SergioRibera/crkbd/pcbs/cherry-wireless/common/left.kicad_sch

## KiCad design pcbs/cherry-wireless/common/left.kicad_sch (2024-08-09)

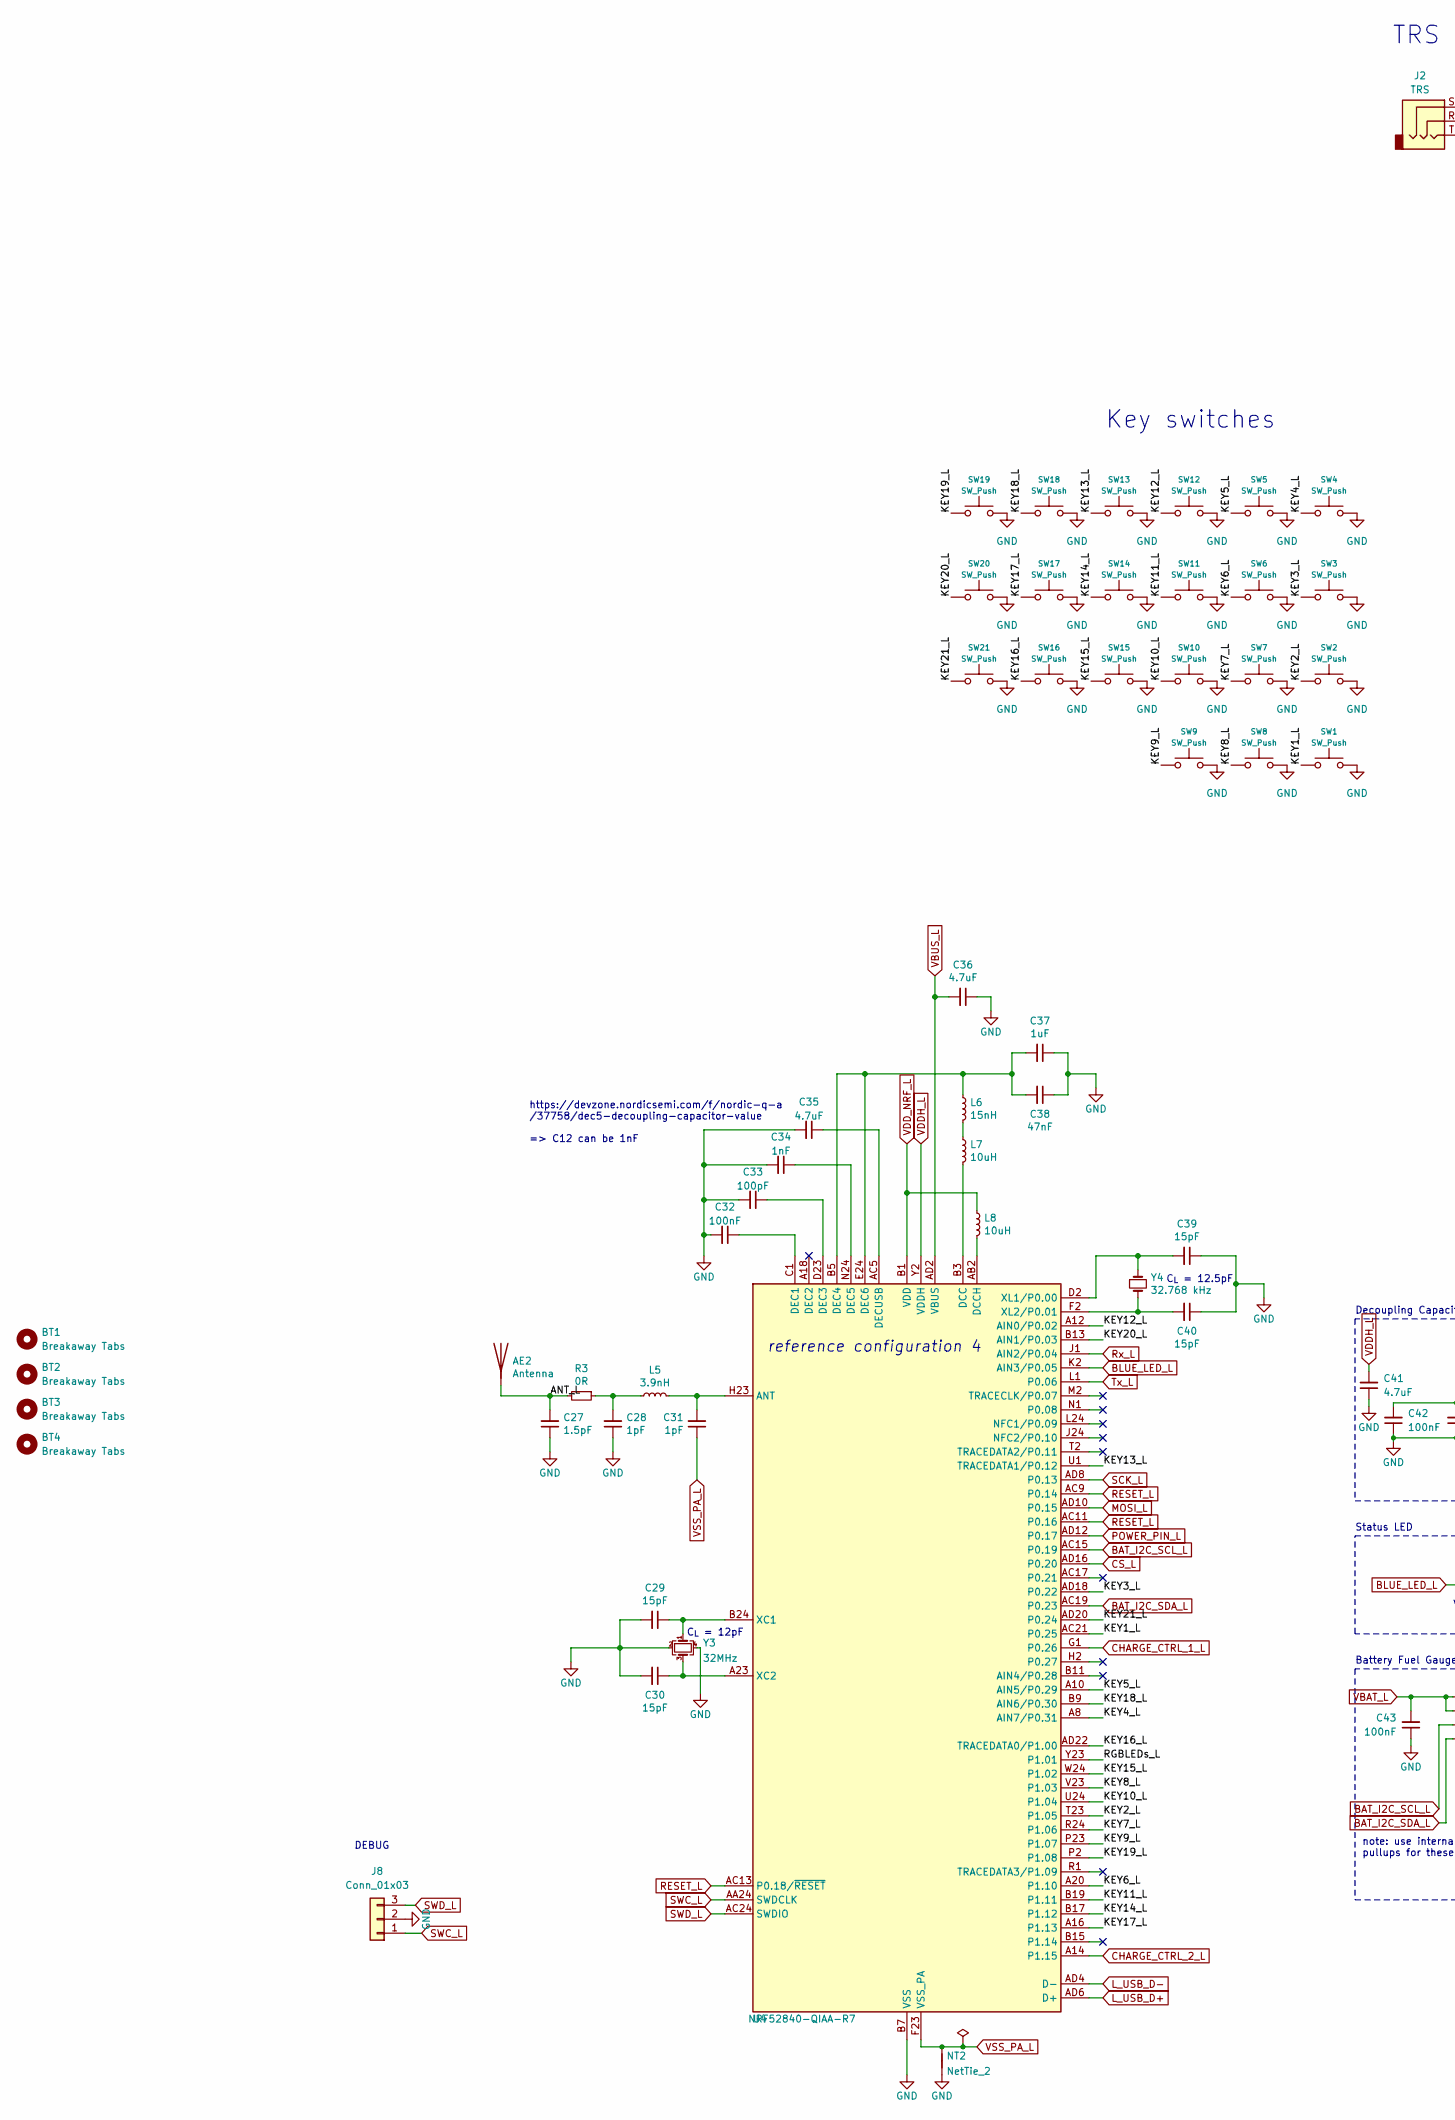
[picture p6: schematic left.kicad_sch, part in row 1, column 1]

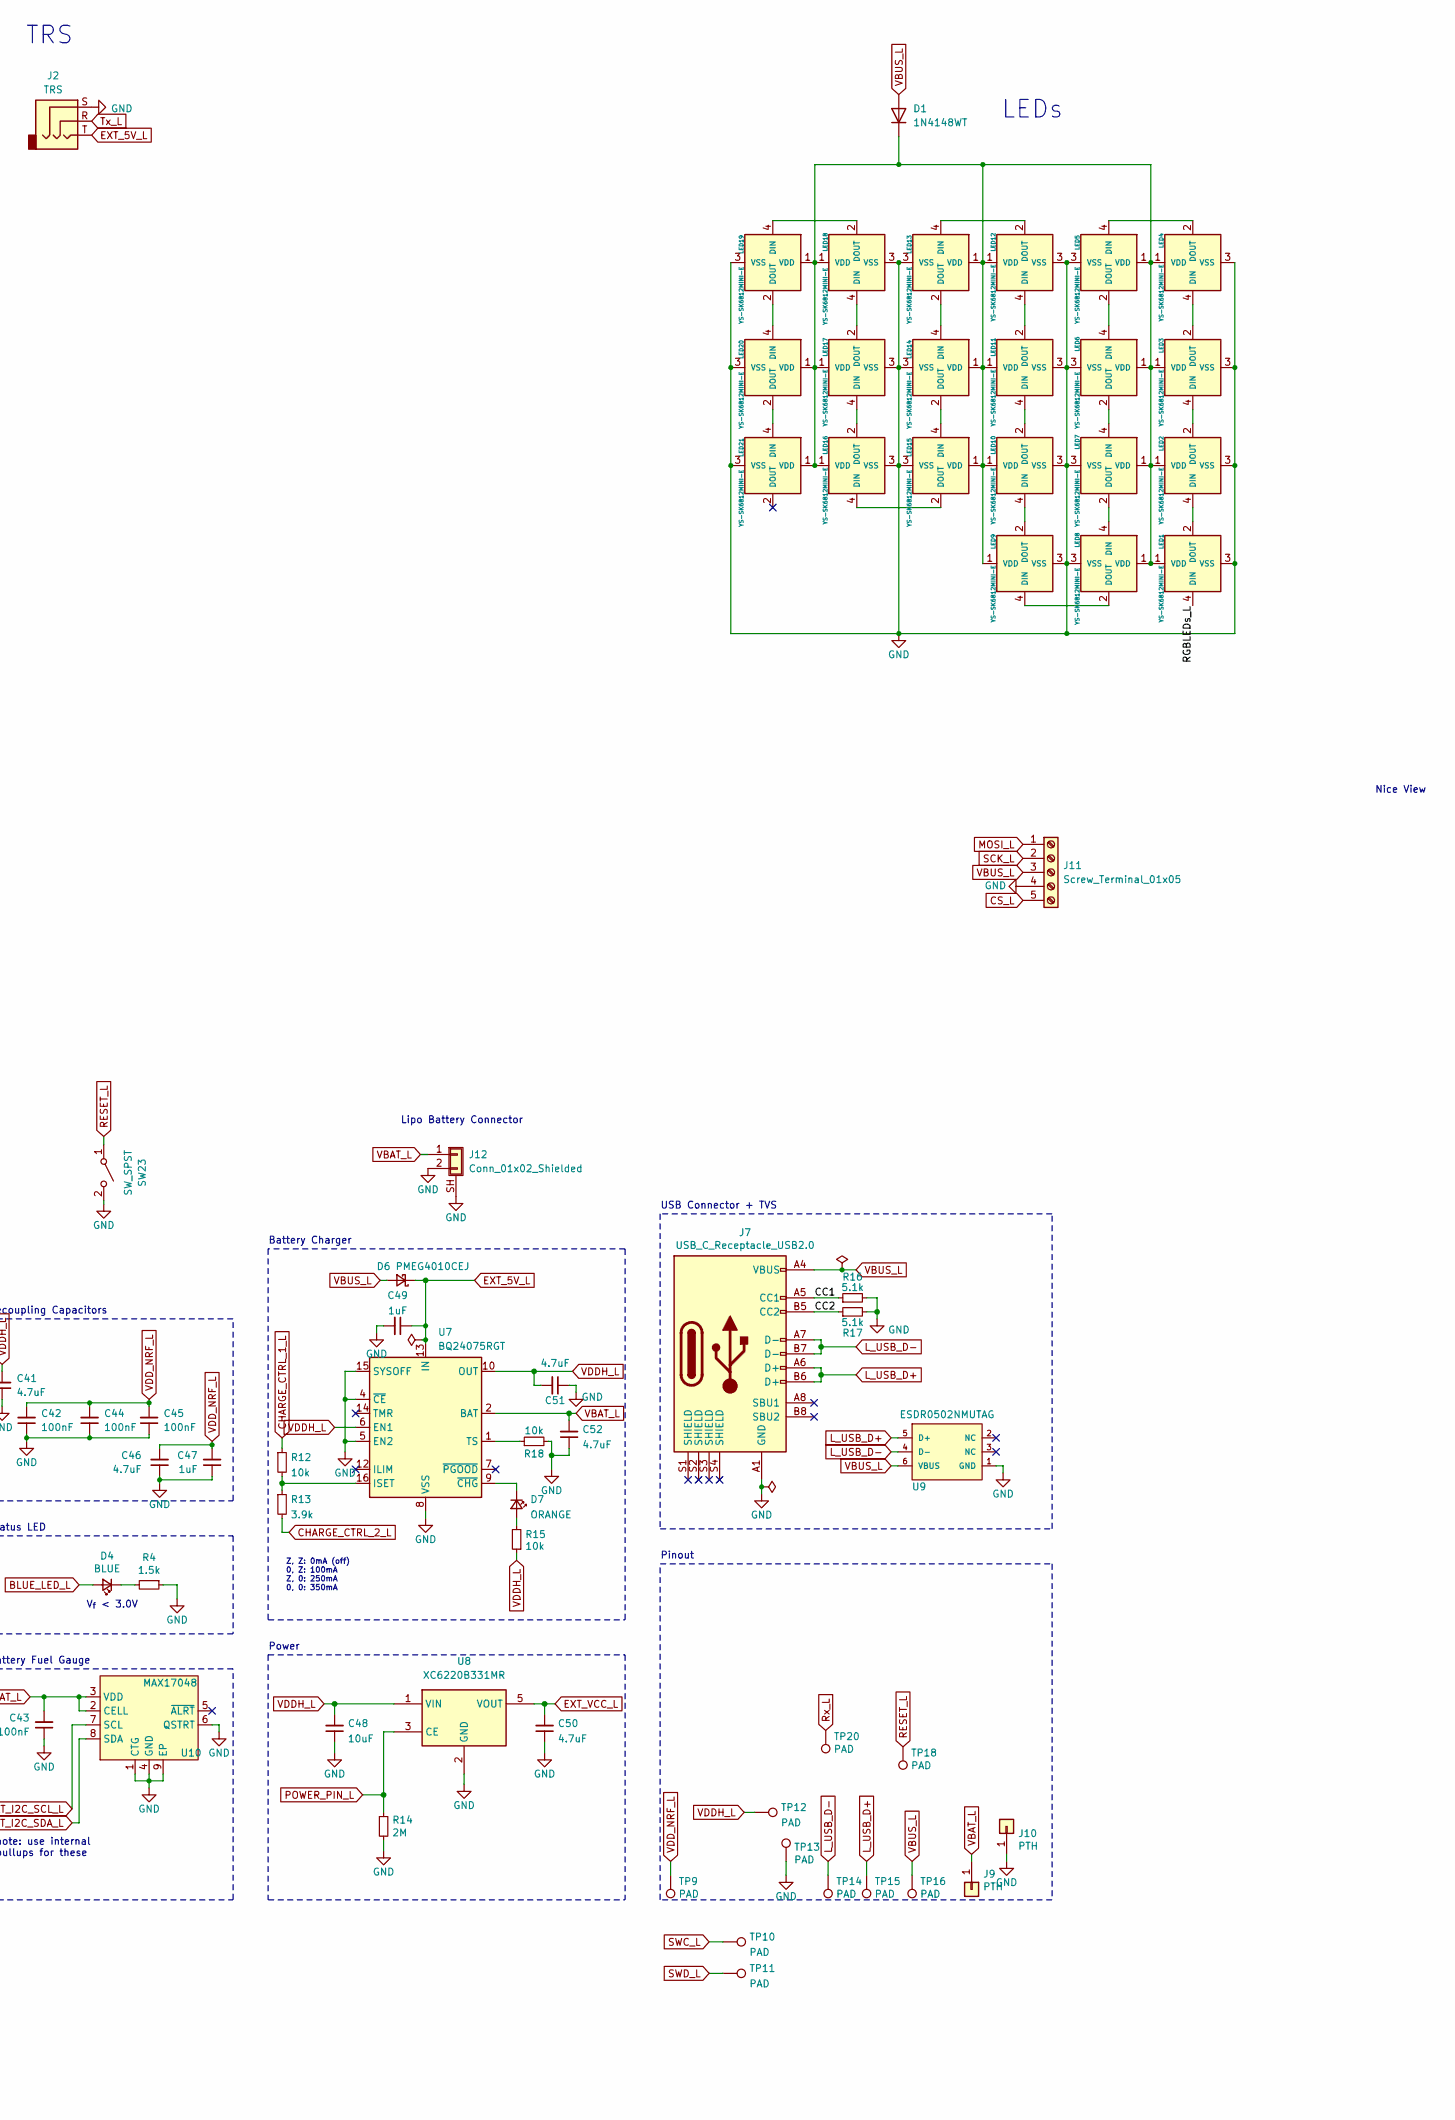
[picture p7: schematic left.kicad_sch, part in row 1, column 2]

Parts:
AE2: Antenna; 2.4GHz-meander-antenna-v2
BT1, BT2, BT3, BT4: Breakaway Tabs; Breakaway_Tabs
C27: 1.5pF; C_0402_1005Metric; JLC Part C1552
C28, C31: 1pF; C_0402_1005Metric; JLC Part C1550
C29, C30, C39, C40: 15pF; C_0402_1005Metric; JLC Part C1548
C32, C42, C43, C44, C45: 100nF; C_0402_1005Metric; JLC Part C1525
C33: 100pF; C_0402_1005Metric; JLC Part C1546
C34: 1nF; C_0402_1005Metric; JLC Part C1523
C35, C36, C41, C46, C50, C51, C52: 4.7uF; C_0402_1005Metric; JLC Part C23733
C37, C47, C49: 1uF; C_0402_1005Metric; JLC Part C52923
C38: 47nF; C_0402_1005Metric; JLC Part C312032
C48: 10uF; C_0603_1608Metric; JLC Part C19702
D1: 1N4148WT; D_SOD-523; JLC Part C232841
D4: BLUE; LED_0402_1005Metric; JLC Part C364550
D6: PMEG4010CEJ; D_SOD-323F; JLC Part C50704
D7: ORANGE; LED_0402_1005Metric; JLC Part C364554
J2: TRS; PJ-398A-5A_PJ-399B-6A; JLC Part C128994
J7: USB_C_Receptacle_USB2.0; USB-C_C168688; JLC Part C168688
J8: Conn_01x03; PinHeader_1x03_P2.54mm_Vertical
J9, J10: PTH; PTH-0.8_0.45mm
J11: Screw_Terminal_01x05; PinHeader_1x05_P2.54mm_Vertical
J12: Conn_01x02_Shielded; CONN-SMD_SM02B-PASS-TLFSN; JLC Part C495198
L5: 3.9nH; L_0402_1005Metric; JLC Part C14033
L6: 15nH; L_0402_1005Metric; JLC Part C27143
L7, L8: 10uH; L_0603_1608Metric; JLC Part C1035
LED1, LED2, LED3, LED4, LED5, LED6, LED7, LED8, LED9, LED10, LED11, LED12, LED13, LED14, LED15, LED16, LED17, LED18, LED19, LED20, LED21: YS-SK6812MINI-E; YS-SK6812MINI-E_crone; JLC Part C5149201
NT2: NetTie_2; net-tie-2-tiny
R3: 0R; R_0402_1005Metric; JLC Part C17168
R4: 1.5k; R_0402_1005Metric; JLC Part C25867
R12, R15, R18: 10k; R_0402_1005Metric; JLC Part C25744
R13: 3.9k; R_0402_1005Metric; JLC Part C51721
R14: 2M; R_0402_1005Metric; JLC Part C138014
R16, R17: 5.1k; R_0402_1005Metric; JLC Part C25905
SW1: SW_Push; keyswitch_cherrymx_hotswap_1.5u; JLC Part C2803348
SW2, SW3, SW4, SW5, SW6, SW7, SW8, SW9, SW10, SW11, SW12, SW13, SW14, SW15, SW16, SW17, SW18, SW19, SW20, SW21: SW_Push; keyswitch_cherrymx_hotswap_1u; JLC Part C2803348
SW23: SW_SPST; SW-SMD-TS-1088-AR02016
TP9, TP10, TP11, TP12, TP13, TP14, TP15, TP16, TP18, TP20: PAD; TestPoint_Pad_1.0x1.0mm-nosilk
U4: NRF52840-QIAA-R7; AQFN-73-1EP_7x7mm_P0.5mm_NRF52840-custom; JLC Part C1851953
U7: BQ24075RGT; VQFN-16-1EP_3x3mm_P0.5mm_EP1.6x1.6mm; JLC Part C2865459
U8: XC6220B331MR; TSOT-23-5; JLC Part C86534
U9: ESDR0502NMUTAG; UDFN-6_1.2x1.0mm_P0.4mm; JLC Part C327480
U10: MAX17048; TDFN-8-1EP_2x2mm_P0.5mm_EP0.8x1.2mm; JLC Part C2682616
Y3: 32MHz; Crystal_SMD_2016-4Pin_2.0x1.6mm; JLC Part C255896
Y4: 32.768 kHz; Crystal_SMD_2012-2Pin_2.0x1.2mm; JLC Part C93231

Connections:
ANT_L: AE2.1, C27.2, R3.2
BAT_I2C_SCL_L: U4.AC15 (P0.19), U10.7 (SCL)
BAT_I2C_SDA_L: U4.AC19 (P0.23), U10.8 (SDA)
BLUE_LED_L: D4.2 (A), U4.K2 (AIN3/P0.05)
CC1: J7.A5 (CC1), R16.1
CC2: J7.B5 (CC2), R17.1
CHARGE_CTRL_1_L: R12.1, U4.G1 (P0.26)
CHARGE_CTRL_2_L: R13.2, U4.A14 (P1.15)
CS_L: J11.5, U4.AD16 (P0.20)
EXT_5V_L: C49.1, D6.1 (K), J2.T, U7.13 (IN)
EXT_VCC_L: C50.2, U8.5 (VOUT)
GND: C27.1, C28.1, C29.2, C30.2, C32.2, C33.2, C34.2, C35.2, C36.1, C37.1, C38.1, C39.1, C40.1, C41.1, C42.1, C43.1, C44.1, C45.1, C46.1, C47.1, C48.1, C49.2, C50.1, C51.1, C52.1, J2.S, J7.A1 (GND), J8.2, J10.1, J11.4, J12.2, J12.SH (Shield), LED1.3 (VSS), LED2.3 (VSS), LED3.3 (VSS), LED4.3 (VSS), LED5.3 (VSS), LED6.3 (VSS), LED7.3 (VSS), LED8.3 (VSS), LED9.3 (VSS), LED10.3 (VSS), LED11.3 (VSS), LED12.3 (VSS), LED13.3 (VSS), LED14.3 (VSS), LED15.3 (VSS), LED16.3 (VSS), LED17.3 (VSS), LED18.3 (VSS), LED19.3 (VSS), LED20.3 (VSS), LED21.3 (VSS), NT2.2, R4.1, R14.2, R16.2, R17.2, R18.2, SW1.2, SW2.2, SW3.2, SW4.2, SW5.2, SW6.2, SW7.2, SW8.2, SW9.2, SW10.2, SW11.2, SW12.2, SW13.2, SW14.2, SW15.2, SW16.2, SW17.2, SW18.2, SW19.2, SW20.2, SW21.2, SW23.2 (B), TP13.1, U4.B7 (VSS), U4.EP (VSS), U7.4 (~CE), U7.5 (EN2), U7.8 (VSS), U7.15 (SYSOFF), U7.17 (VSS), U8.2 (GND), U9.1 (GND), U10.1 (CTG), U10.4 (GND), U10.6 (QSTRT), U10.9 (EP), Y3.2, Y3.4
KEY1_L: SW1.1, U4.AC21 (P0.25)
KEY2_L: SW2.1, U4.T23 (P1.05)
KEY3_L: SW3.1, U4.AD18 (P0.22)
KEY4_L: SW4.1, U4.A8 (AIN7/P0.31)
KEY5_L: SW5.1, U4.A10 (AIN5/P0.29)
KEY6_L: SW6.1, U4.A20 (P1.10)
KEY7_L: SW7.1, U4.R24 (P1.06)
KEY8_L: SW8.1, U4.V23 (P1.03)
KEY9_L: SW9.1, U4.P23 (P1.07)
KEY10_L: SW10.1, U4.U24 (P1.04)
KEY11_L: SW11.1, U4.B19 (P1.11)
KEY12_L: SW12.1, U4.A12 (AIN0/P0.02)
KEY13_L: SW13.1, U4.U1 (TRACEDATA1/P0.12)
KEY14_L: SW14.1, U4.B17 (P1.12)
KEY15_L: SW15.1, U4.W24 (P1.02)
KEY16_L: SW16.1, U4.AD22 (TRACEDATA0/P1.00)
KEY17_L: SW17.1, U4.A16 (P1.13)
KEY18_L: SW18.1, U4.B9 (AIN6/P0.30)
KEY19_L: SW19.1, U4.P2 (P1.08)
KEY20_L: SW20.1, U4.B13 (AIN1/P0.03)
KEY21_L: SW21.1, U4.AD20 (P0.24)
L_USB_D+: J7.A6 (D+), J7.B6 (D+), TP15.1, U4.AD6 (D+), U9.5 (D+)
L_USB_D-: J7.A7 (D-), J7.B7 (D-), TP14.1, U4.AD4 (D-), U9.4 (D-)
MOSI_L: J11.1, U4.AD10 (P0.15)
unnamed: C28.2, L5.1, R3.1
unnamed: C29.1, U4.B24 (XC1), Y3.1
unnamed: C30.1, U4.A23 (XC2), Y3.3
unnamed: C31.2, L5.2, U4.H23 (ANT)
unnamed: C32.1, U4.C1 (DEC1)
unnamed: C33.1, U4.D23 (DEC3)
unnamed: C34.1, U4.N24 (DEC5)
unnamed: C35.1, U4.AC5 (DECUSB)
unnamed: C37.2, C38.2, L6.1, U4.B5 (DEC4), U4.E24 (DEC6)
unnamed: C39.2, U4.D2 (XL1/P0.00), Y4.1
unnamed: C40.2, U4.F2 (XL2/P0.01), Y4.2
unnamed: D1.1 (K), LED1.1 (VDD), LED2.1 (VDD), LED3.1 (VDD), LED4.1 (VDD), LED5.1 (VDD), LED6.1 (VDD), LED7.1 (VDD), LED8.1 (VDD), LED9.1 (VDD), LED10.1 (VDD), LED11.1 (VDD), LED12.1 (VDD), LED13.1 (VDD), LED14.1 (VDD), LED15.1 (VDD), LED16.1 (VDD), LED17.1 (VDD), LED18.1 (VDD), LED19.1 (VDD), LED20.1 (VDD), LED21.1 (VDD)
unnamed: D4.1 (K), R4.2
unnamed: D7.1 (K), U7.9 (~CHG)
unnamed: D7.2 (A), R15.2
unnamed: L6.2, L7.1
unnamed: L7.2, U4.B3 (DCC)
unnamed: L8.2, U4.AB2 (DCCH)
unnamed: LED1.2 (DOUT), LED2.4 (DIN)
unnamed: LED2.2 (DOUT), LED3.4 (DIN)
unnamed: LED3.2 (DOUT), LED4.4 (DIN)
unnamed: LED4.2 (DOUT), LED5.4 (DIN)
unnamed: LED5.2 (DOUT), LED6.4 (DIN)
unnamed: LED6.2 (DOUT), LED7.4 (DIN)
unnamed: LED7.2 (DOUT), LED8.4 (DIN)
unnamed: LED8.2 (DOUT), LED9.4 (DIN)
unnamed: LED10.2 (DOUT), LED11.4 (DIN)
unnamed: LED9.2 (DOUT), LED10.4 (DIN)
unnamed: LED11.2 (DOUT), LED12.4 (DIN)
unnamed: LED12.2 (DOUT), LED13.4 (DIN)
unnamed: LED13.2 (DOUT), LED14.4 (DIN)
unnamed: LED14.2 (DOUT), LED15.4 (DIN)
unnamed: LED15.2 (DOUT), LED16.4 (DIN)
unnamed: LED16.2 (DOUT), LED17.4 (DIN)
unnamed: LED17.2 (DOUT), LED18.4 (DIN)
unnamed: LED18.2 (DOUT), LED19.4 (DIN)
unnamed: LED19.2 (DOUT), LED20.4 (DIN)
unnamed: LED20.2 (DOUT), LED21.4 (DIN)
unnamed: R12.2, R13.1, U7.16 (ISET)
unnamed: R18.1, U7.1 (TS)
POWER_PIN_L: R14.1, U4.AD12 (P0.17), U8.3 (CE)
RESET_L: SW23.1 (A), TP18.1, U4.AC9 (P0.14), U4.AC11 (P0.16), U4.AC13 (P0.18/~RESET)
RGBLEDs_L: LED1.4 (DIN), U4.Y23 (P1.01)
Rx_L: TP20.1, U4.J1 (AIN2/P0.04)
SCK_L: J11.2, U4.AD8 (P0.13)
SWC_L: J8.1, TP10.1, U4.AA24 (SWDCLK)
SWD_L: J8.3, TP11.1, U4.AC24 (SWDIO)
Tx_L: J2.R, U4.L1 (P0.06)
VBAT_L: C43.2, C52.2, J9.1, J12.1, U7.2 (BAT), U7.3 (BAT), U10.2 (CELL), U10.3 (VDD)
VBUS_L: C36.2, D1.2 (A), D6.2 (A), J7.A4 (VBUS), J11.3, TP16.1, U4.AD2 (VBUS), U9.6 (VBUS)
VDDH_L: C41.2, C48.2, C51.2, R15.1, TP12.1, U4.Y2 (VDDH), U7.6 (EN1), U7.10 (OUT), U7.11 (OUT), U8.1 (VIN)
VDD_NRF_L: C42.2, C44.2, C45.2, C46.2, C47.2, L8.1, TP9.1, U4.A22 (VDD), U4.AD14 (VDD), U4.AD23 (VDD), U4.B1 (VDD), U4.W1 (VDD)
VSS_PA_L: C31.1, NT2.1, U4.F23 (VSS_PA)

Notes on the sheet:
Key switches
Battery Fuel Gauge
C_{L} = 12pF
Status LED
Z, Z: 0mA (off) 0, Z: 100mA Z, 0: 250mA 0, 0: 350mA
Lipo Battery Connector
DEBUG
LEDs
note: use internal pullups for these
V_{f} < 3.0V
https://devzone.nordicsemi.com/f/nordic-q-a /37758/dec5-decoupling-capacitor-value => C12 can be 1nF
Decoupling Capacitors
Pinout
TRS
C_{L} = 12.5pF
Power
Battery Charger
Nice View
USB Connector + TVS
reference configuration 4
