SergioRibera/crkbd/pcbs/cherry-wireless/common/right.kicad_sch

## KiCad design pcbs/cherry-wireless/common/right.kicad_sch (2024-08-09)

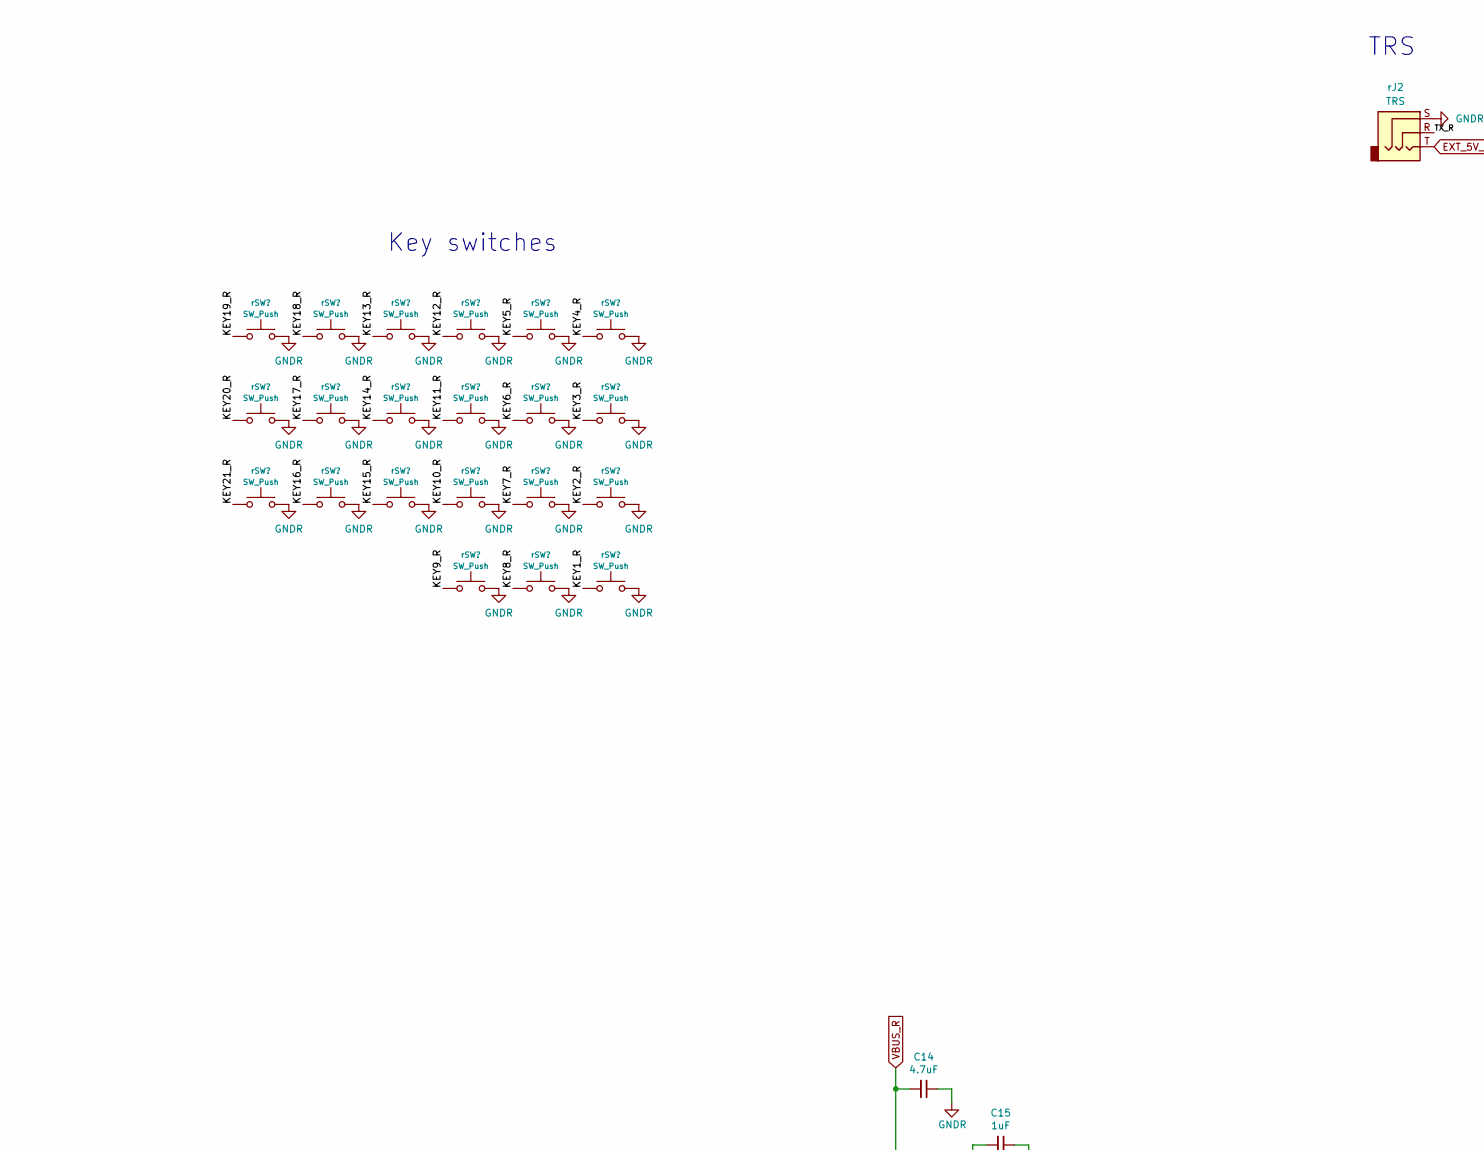
[picture p8: schematic right.kicad_sch, part in row 1, column 1]

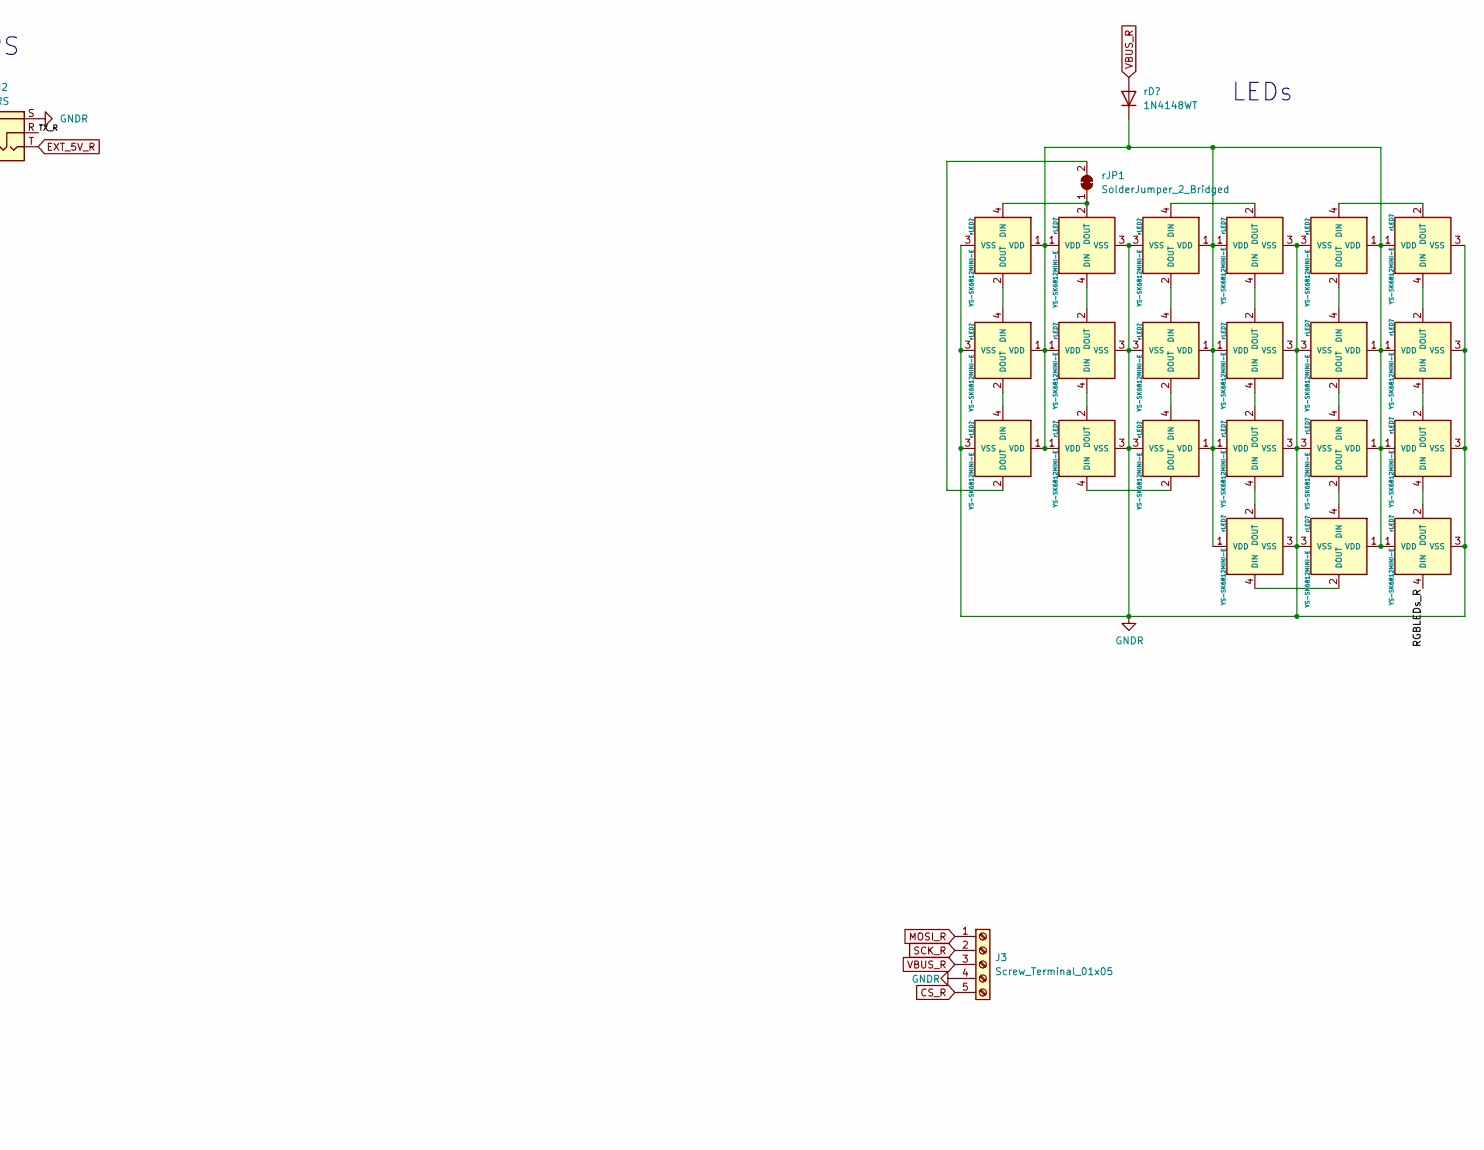
[picture p9: schematic right.kicad_sch, part in row 1, column 2]

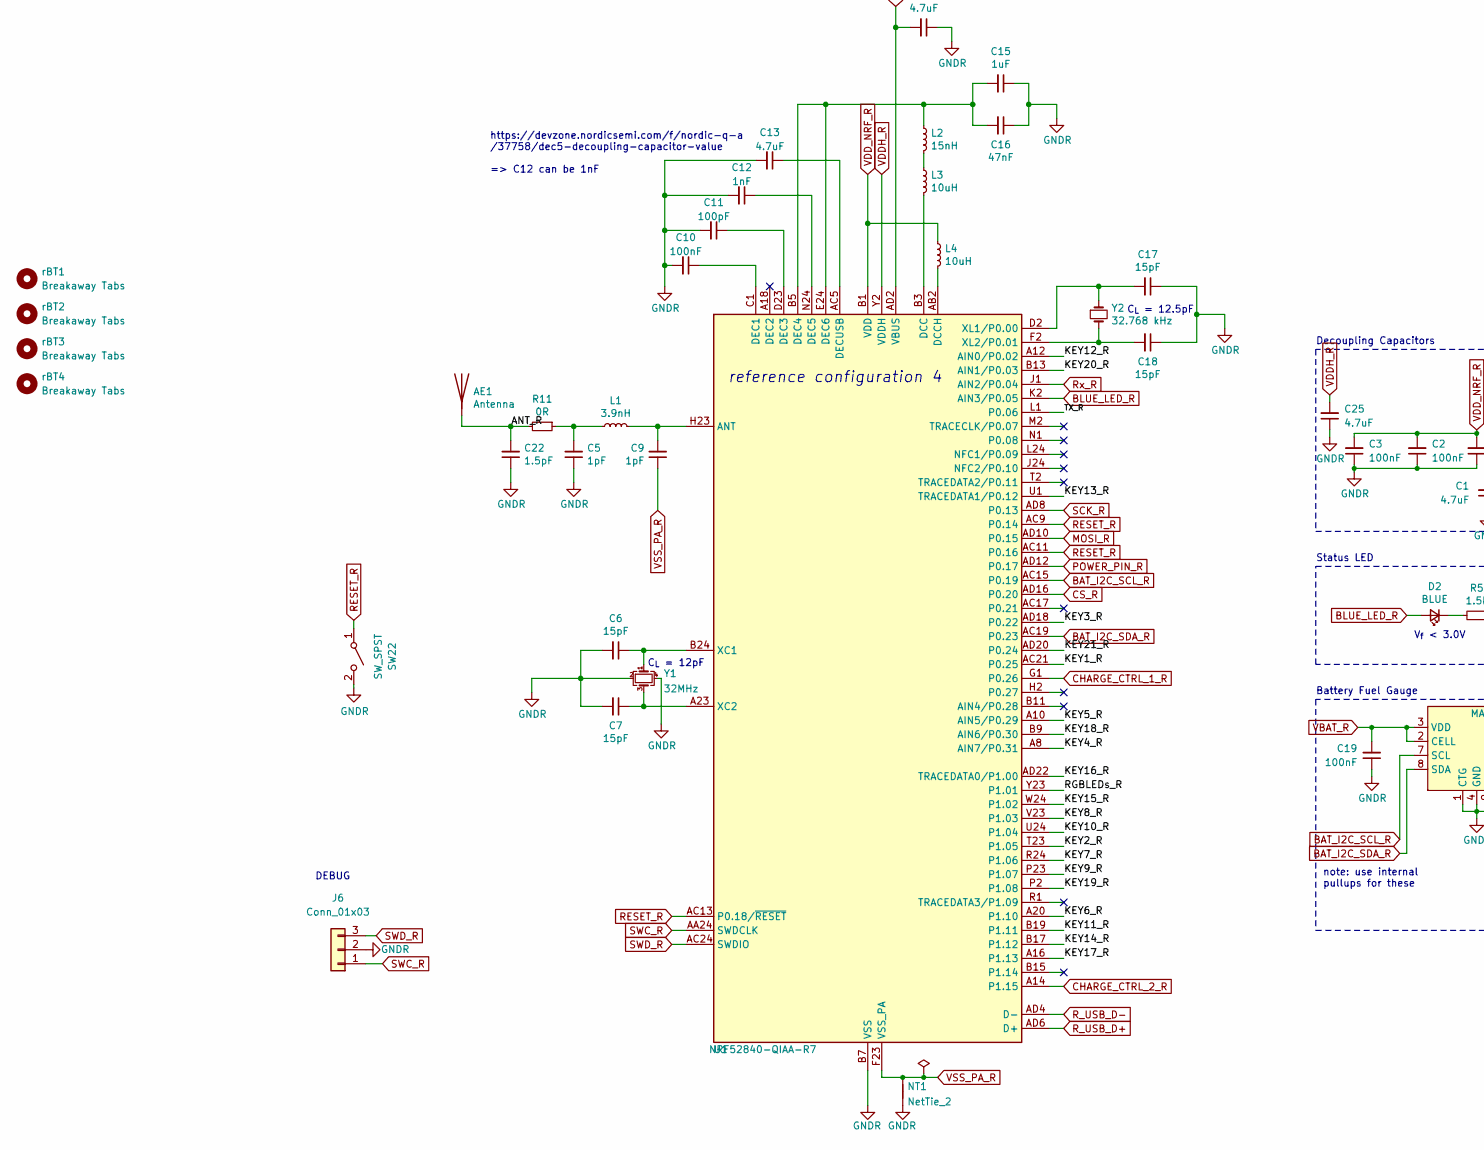
[picture p10: schematic right.kicad_sch, part in row 2, column 1]

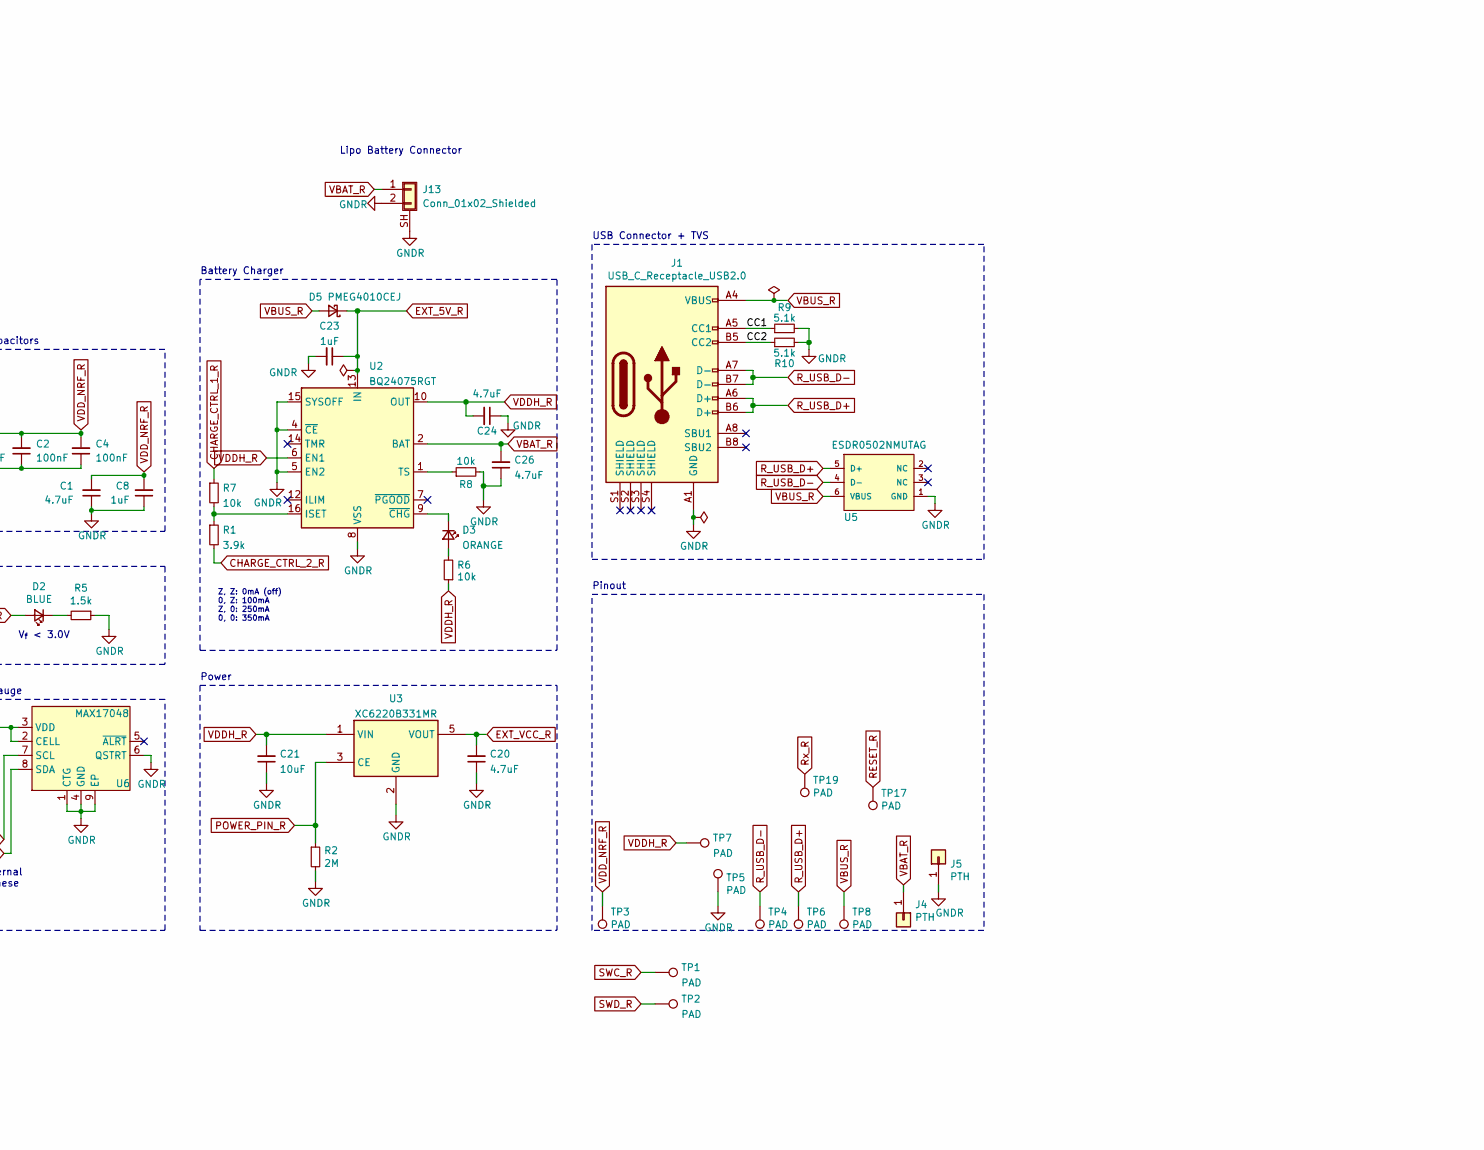
[picture p11: schematic right.kicad_sch, part in row 2, column 2]

Parts:
AE1: Antenna; 2.4GHz-meander-antenna-v2
C1, C13, C14, C20, C24, C25, C26: 4.7uF; C_0402_1005Metric; JLC Part C23733
C2, C3, C4, C10, C19: 100nF; C_0402_1005Metric; JLC Part C1525
C5, C9: 1pF; C_0402_1005Metric; JLC Part C1550
C6, C7, C17, C18: 15pF; C_0402_1005Metric; JLC Part C1548
C8, C15, C23: 1uF; C_0402_1005Metric; JLC Part C52923
C11: 100pF; C_0402_1005Metric; JLC Part C1546
C12: 1nF; C_0402_1005Metric; JLC Part C1523
C16: 47nF; C_0402_1005Metric; JLC Part C312032
C21: 10uF; C_0603_1608Metric; JLC Part C19702
C22: 1.5pF; C_0402_1005Metric; JLC Part C1552
D2: BLUE; LED_0402_1005Metric; JLC Part C364550
D3: ORANGE; LED_0402_1005Metric; JLC Part C364554
D5: PMEG4010CEJ; D_SOD-323F; JLC Part C50704
J1: USB_C_Receptacle_USB2.0; USB-C_C168688; JLC Part C168688
J3: Screw_Terminal_01x05; PinHeader_1x05_P2.54mm_Vertical
J4, J5: PTH; PTH-0.8_0.45mm
J6: Conn_01x03; PinHeader_1x03_P2.54mm_Vertical
J13: Conn_01x02_Shielded; CONN-SMD_SM02B-PASS-TLFSN; JLC Part C495198
L1: 3.9nH; L_0402_1005Metric; JLC Part C14033
L2: 15nH; L_0402_1005Metric; JLC Part C27143
L3, L4: 10uH; L_0603_1608Metric; JLC Part C1035
NT1: NetTie_2; net-tie-2-tiny
R1: 3.9k; R_0402_1005Metric; JLC Part C51721
R2: 2M; R_0402_1005Metric; JLC Part C138014
R5: 1.5k; R_0402_1005Metric; JLC Part C25867
R6, R7, R8: 10k; R_0402_1005Metric; JLC Part C25744
R9, R10: 5.1k; R_0402_1005Metric; JLC Part C25905
R11: 0R; R_0402_1005Metric; JLC Part C17168
SW22: SW_SPST; SW-SMD-TS-1088-AR02016
TP1, TP2, TP3, TP4, TP5, TP6, TP7, TP8, TP17, TP19: PAD; TestPoint_Pad_1.0x1.0mm-nosilk
U1: NRF52840-QIAA-R7; AQFN-73-1EP_7x7mm_P0.5mm_NRF52840-custom; JLC Part C1851953
U2: BQ24075RGT; VQFN-16-1EP_3x3mm_P0.5mm_EP1.6x1.6mm; JLC Part C2865459
U3: XC6220B331MR; TSOT-23-5; JLC Part C86534
U5: ESDR0502NMUTAG; UDFN-6_1.2x1.0mm_P0.4mm; JLC Part C327480
U6: MAX17048; TDFN-8-1EP_2x2mm_P0.5mm_EP0.8x1.2mm; JLC Part C2682616
Y1: 32MHz; Crystal_SMD_2016-4Pin_2.0x1.6mm; JLC Part C255896
Y2: 32.768 kHz; Crystal_SMD_2012-2Pin_2.0x1.2mm; JLC Part C93231
rBT1, rBT2, rBT3, rBT4: Breakaway Tabs; Breakaway_Tabs
rD1: 1N4148WT; D_SOD-523; JLC Part C232841
rJ2: TRS; PJ-398A-5A_PJ-399B-6A; JLC Part C128994
rJP1: SolderJumper_2_Bridged; SolderJumper-2_P1.3mm_Open_RoundedPad1.0x1.5mm
rLED1, rLED2, rLED3, rLED4, rLED5, rLED6, rLED7, rLED8, rLED9, rLED10, rLED11, rLED12, rLED13, rLED14, rLED15, rLED16, rLED17, rLED18, rLED19, rLED20, rLED21: YS-SK6812MINI-E; YS-SK6812MINI-E_crone; JLC Part C5149201
rSW1: SW_Push; keyswitch_cherrymx_hotswap_1.5u; JLC Part C2803348
rSW2, rSW3, rSW4, rSW5, rSW6, rSW7, rSW8, rSW9, rSW10, rSW11, rSW12, rSW13, rSW14, rSW15, rSW16, rSW17, rSW18, rSW19, rSW20, rSW21: SW_Push; keyswitch_cherrymx_hotswap_1u; JLC Part C2803348

Connections:
ANT_R: AE1.1, C22.2, R11.2
BAT_I2C_SCL_R: U1.AC15 (P0.19), U6.7 (SCL)
BAT_I2C_SDA_R: U1.AC19 (P0.23), U6.8 (SDA)
BLUE_LED_R: D2.2 (A), U1.K2 (AIN3/P0.05)
CC1: J1.A5 (CC1), R9.1
CC2: J1.B5 (CC2), R10.1
CHARGE_CTRL_1_R: R7.1, U1.G1 (P0.26)
CHARGE_CTRL_2_R: R1.2, U1.A14 (P1.15)
CS_R: J3.5, U1.AD16 (P0.20)
EXT_5V_R: C23.1, D5.1 (K), U2.13 (IN), rJ2.T
EXT_VCC_R: C20.2, U3.5 (VOUT)
GNDR: C1.1, C2.1, C3.1, C4.1, C5.1, C6.2, C7.2, C8.1, C10.2, C11.2, C12.2, C13.2, C14.1, C15.1, C16.1, C17.1, C18.1, C19.1, C20.1, C21.1, C22.1, C23.2, C24.1, C25.1, C26.1, J1.A1 (GND), J3.4, J5.1, J6.2, J13.2, J13.SH (Shield), NT1.2, R2.2, R5.1, R8.2, R9.2, R10.2, SW22.2 (B), TP5.1, U1.B7 (VSS), U1.EP (VSS), U2.4 (~CE), U2.5 (EN2), U2.8 (VSS), U2.15 (SYSOFF), U2.17 (VSS), U3.2 (GND), U5.1 (GND), U6.1 (CTG), U6.4 (GND), U6.6 (QSTRT), U6.9 (EP), Y1.2, Y1.4, rJ2.S, rLED1.3 (VSS), rLED2.3 (VSS), rLED3.3 (VSS), rLED4.3 (VSS), rLED5.3 (VSS), rLED6.3 (VSS), rLED7.3 (VSS), rLED8.3 (VSS), rLED9.3 (VSS), rLED10.3 (VSS), rLED11.3 (VSS), rLED12.3 (VSS), rLED13.3 (VSS), rLED14.3 (VSS), rLED15.3 (VSS), rLED16.3 (VSS), rLED17.3 (VSS), rLED18.3 (VSS), rLED19.3 (VSS), rLED20.3 (VSS), rLED21.3 (VSS), rSW1.2, rSW2.2, rSW3.2, rSW4.2, rSW5.2, rSW6.2, rSW7.2, rSW8.2, rSW9.2, rSW10.2, rSW11.2, rSW12.2, rSW13.2, rSW14.2, rSW15.2, rSW16.2, rSW17.2, rSW18.2, rSW19.2, rSW20.2, rSW21.2
KEY1_R: U1.AC21 (P0.25), rSW1.1
KEY2_R: U1.T23 (P1.05), rSW2.1
KEY3_R: U1.AD18 (P0.22), rSW3.1
KEY4_R: U1.A8 (AIN7/P0.31), rSW4.1
KEY5_R: U1.A10 (AIN5/P0.29), rSW5.1
KEY6_R: U1.A20 (P1.10), rSW6.1
KEY7_R: U1.R24 (P1.06), rSW7.1
KEY8_R: U1.V23 (P1.03), rSW8.1
KEY9_R: U1.P23 (P1.07), rSW9.1
KEY10_R: U1.U24 (P1.04), rSW10.1
KEY11_R: U1.B19 (P1.11), rSW11.1
KEY12_R: U1.A12 (AIN0/P0.02), rSW12.1
KEY13_R: U1.U1 (TRACEDATA1/P0.12), rSW13.1
KEY14_R: U1.B17 (P1.12), rSW14.1
KEY15_R: U1.W24 (P1.02), rSW15.1
KEY16_R: U1.AD22 (TRACEDATA0/P1.00), rSW16.1
KEY17_R: U1.A16 (P1.13), rSW17.1
KEY18_R: U1.B9 (AIN6/P0.30), rSW18.1
KEY19_R: U1.P2 (P1.08), rSW19.1
KEY20_R: U1.B13 (AIN1/P0.03), rSW20.1
KEY21_R: U1.AD20 (P0.24), rSW21.1
MOSI_R: J3.1, U1.AD10 (P0.15)
unnamed: C5.2, L1.1, R11.1
unnamed: C6.1, U1.B24 (XC1), Y1.1
unnamed: C7.1, U1.A23 (XC2), Y1.3
unnamed: C9.2, L1.2, U1.H23 (ANT)
unnamed: C10.1, U1.C1 (DEC1)
unnamed: C11.1, U1.D23 (DEC3)
unnamed: C12.1, U1.N24 (DEC5)
unnamed: C13.1, U1.AC5 (DECUSB)
unnamed: C15.2, C16.2, L2.1, U1.B5 (DEC4), U1.E24 (DEC6)
unnamed: C17.2, U1.D2 (XL1/P0.00), Y2.1
unnamed: C18.2, U1.F2 (XL2/P0.01), Y2.2
unnamed: D2.1 (K), R5.2
unnamed: D3.1 (K), U2.9 (~CHG)
unnamed: D3.2 (A), R6.2
unnamed: L2.2, L3.1
unnamed: L3.2, U1.B3 (DCC)
unnamed: L4.2, U1.AB2 (DCCH)
unnamed: R1.1, R7.2, U2.16 (ISET)
unnamed: R8.1, U2.1 (TS)
unnamed: rD1.1 (K), rLED1.1 (VDD), rLED2.1 (VDD), rLED3.1 (VDD), rLED4.1 (VDD), rLED5.1 (VDD), rLED6.1 (VDD), rLED7.1 (VDD), rLED8.1 (VDD), rLED9.1 (VDD), rLED10.1 (VDD), rLED11.1 (VDD), rLED12.1 (VDD), rLED13.1 (VDD), rLED14.1 (VDD), rLED15.1 (VDD), rLED16.1 (VDD), rLED17.1 (VDD), rLED18.1 (VDD), rLED19.1 (VDD), rLED20.1 (VDD), rLED21.1 (VDD)
unnamed: rJP1.1 (A), rLED18.2 (DOUT), rLED19.4 (DIN)
unnamed: rJP1.2 (B), rLED21.2 (DOUT)
unnamed: rLED1.2 (DOUT), rLED2.4 (DIN)
unnamed: rLED2.2 (DOUT), rLED3.4 (DIN)
unnamed: rLED3.2 (DOUT), rLED4.4 (DIN)
unnamed: rLED4.2 (DOUT), rLED5.4 (DIN)
unnamed: rLED5.2 (DOUT), rLED6.4 (DIN)
unnamed: rLED6.2 (DOUT), rLED7.4 (DIN)
unnamed: rLED7.2 (DOUT), rLED8.4 (DIN)
unnamed: rLED8.2 (DOUT), rLED9.4 (DIN)
unnamed: rLED10.2 (DOUT), rLED11.4 (DIN)
unnamed: rLED9.2 (DOUT), rLED10.4 (DIN)
unnamed: rLED11.2 (DOUT), rLED12.4 (DIN)
unnamed: rLED12.2 (DOUT), rLED13.4 (DIN)
unnamed: rLED13.2 (DOUT), rLED14.4 (DIN)
unnamed: rLED14.2 (DOUT), rLED15.4 (DIN)
unnamed: rLED15.2 (DOUT), rLED16.4 (DIN)
unnamed: rLED16.2 (DOUT), rLED17.4 (DIN)
unnamed: rLED17.2 (DOUT), rLED18.4 (DIN)
unnamed: rLED19.2 (DOUT), rLED20.4 (DIN)
unnamed: rLED20.2 (DOUT), rLED21.4 (DIN)
POWER_PIN_R: R2.1, U1.AD12 (P0.17), U3.3 (CE)
RESET_R: SW22.1 (A), TP17.1, U1.AC9 (P0.14), U1.AC11 (P0.16), U1.AC13 (P0.18/~RESET)
RGBLEDs_R: U1.Y23 (P1.01), rLED1.4 (DIN)
R_USB_D+: J1.A6 (D+), J1.B6 (D+), TP6.1, U1.AD6 (D+), U5.5 (D+)
R_USB_D-: J1.A7 (D-), J1.B7 (D-), TP4.1, U1.AD4 (D-), U5.4 (D-)
Rx_R: TP19.1, U1.J1 (AIN2/P0.04)
SCK_R: J3.2, U1.AD8 (P0.13)
SWC_R: J6.1, TP1.1, U1.AA24 (SWDCLK)
SWD_R: J6.3, TP2.1, U1.AC24 (SWDIO)
TX_R: U1.L1 (P0.06), rJ2.R
VBAT_R: C19.2, C26.2, J4.1, J13.1, U2.2 (BAT), U2.3 (BAT), U6.2 (CELL), U6.3 (VDD)
VBUS_R: C14.2, D5.2 (A), J1.A4 (VBUS), J3.3, TP8.1, U1.AD2 (VBUS), U5.6 (VBUS), rD1.2 (A)
VDDH_R: C21.2, C24.2, C25.2, R6.1, TP7.1, U1.Y2 (VDDH), U2.6 (EN1), U2.10 (OUT), U2.11 (OUT), U3.1 (VIN)
VDD_NRF_R: C1.2, C2.2, C3.2, C4.2, C8.2, L4.1, TP3.1, U1.A22 (VDD), U1.AD14 (VDD), U1.AD23 (VDD), U1.B1 (VDD), U1.W1 (VDD)
VSS_PA_R: C9.1, NT1.1, U1.F23 (VSS_PA)

Notes on the sheet:
Battery Charger
TRS
Z, Z: 0mA (off) 0, Z: 100mA Z, 0: 250mA 0, 0: 350mA
Decoupling Capacitors
C_{L} = 12.5pF
Power
note: use internal pullups for these
V_{f} < 3.0V
Key switches
LEDs
DEBUG
Status LED
C_{L} = 12pF
Lipo Battery Connector
USB Connector + TVS
reference configuration 4
Battery Fuel Gauge
https://devzone.nordicsemi.com/f/nordic-q-a /37758/dec5-decoupling-capacitor-value => C12 can be 1nF
Pinout
